jaisor/ProtoPuck32/src/WifiManager.cpp

#if !( defined(ESP32) )
  #error This code is intended to run on ESP32 platform! Please check your Tools->Board setting.
#endif

#include <Arduino.h>
#include <WiFiClient.h>
#include <esp_wifi.h>
#include <ezTime.h>
#include <AsyncElegantOTA.h>
#include <StreamUtils.h>

#include "WifiManager.h"
#include "Configuration.h"

#define MAX_CONNECT_TIMEOUT_MS 15000 // seconds to connect before creating its own AP
#define BOARD_LED_PIN 2

const int RSSI_MAX =-50;// define maximum straighten of signal in dBm
const int RSSI_MIN =-100;// define minimum strength of signal in dBm

WiFiClient espClient;

int dBmtoPercentage(int dBm) {
  int quality;
  if(dBm <= RSSI_MIN) {
  quality = 0;
  } else if(dBm >= RSSI_MAX) {  
  quality = 100;
  } else {
  quality = 2 * (dBm + 100);
  }
  return quality;
}

const unsigned char icon_wifi [] PROGMEM = {
  0x00, 0x00, 0x70, 0x00, 0x7e, 0x00, 0x07, 0x80, 0x01, 0xc0, 0x70, 0xe0, 0x7c, 0x30, 0x0e, 0x38, 
  0x03, 0x18, 0x61, 0x8c, 0x78, 0xcc, 0x1c, 0xc4, 0x0c, 0x66, 0x46, 0x66, 0x66, 0x66, 0x00, 0x00
};

const unsigned char icon_ip [] PROGMEM = {
  0x0, 0xee, 0x49, 0x49, 0x4e, 0x48, 0xe8, 0x0
};

const String htmlTop FL_PROGMEM = "<html>\
  <head>\
  <title>%s</title>\
  <style>\
    body { background-color: #303030; font-family: 'Anaheim',sans-serif; Color: #d8d8d8; }\
  </style>\
  </head>\
  <body>\
  <h1>%s ProtoPuck32</h1>";

const String htmlBottom FL_PROGMEM = "<br><br><hr>\
  <p>Uptime: %02d:%02d:%02d | Device time: %s | Device: %s</p>\
  %s\
  <form method='POST' action='/factory_reset' enctype='application/x-www-form-urlencoded'>\
    <input type='submit' style='font-size: 6pt; color: red; background-color: black;' value='Factory Reset...'>\
  </form>\
  </body>\
</html>";

const String htmlWifiApConnectForm FL_PROGMEM = "<h2>Connect to WiFi Access Point (AP)</h2>\
  <form method='POST' action='/connect' enctype='application/x-www-form-urlencoded'>\
    <label for='ssid'>SSID (AP Name):</label><br>\
    <input type='text' id='ssid' name='ssid'><br><br>\
    <label for='pass'>Password (WPA2):</label><br>\
    <input type='password' id='pass' name='password' minlength='8' autocomplete='off' required><br><br>\
    <input type='submit' value='Connect...'>\
  </form>";

const String htmlDeviceConfigs FL_PROGMEM = "<hr><h2>Configs</h2>\
  <form method='POST' action='/config' enctype='application/x-www-form-urlencoded'>\
    <label for='deviceName'>Device name:</label><br>\
    <input type='text' id='deviceName' name='deviceName' value='%s'><br>\
    <br>\
    <label for='mqttServer'>MQTT Server:</label><br>\
    <input type='text' id='mqttServer' name='mqttServer' value='%s'><br>\
    <label for='mqttPort'>MQTT Port:</label><br>\
    <input type='text' id='mqttPort' name='mqttPort' value='%i'><br>\
    <label for='mqttTopic'>MQTT Topic:</label><br>\
    <input type='text' id='mqttTopic' name='mqttTopic' value='%s'><br>\
    <br>\
    <label for='ntpServer'>NTP Server:</label><br>\
    <input type='text' id='ntpServer' name='ntpServer' value='%s'><br>\
    <label for='gmtOffset_sec'>GMT Offset:</label><br>\
    <input type='text' id='gmtOffset_sec' name='gmtOffset_sec' value='%li'> sec.<br>\
    <label for='daylightOffset_sec'>Daylight Offset:</label><br>\
    <input type='text' id='daylightOffset_sec' name='daylightOffset_sec' value='%i'> sec.<br>\
    <br>\
    <input type='submit' value='Set...'>\
  </form>";

char _deviceId[32];
char *getDeviceId() {
  
  uint32_t chipId = 0;
  for(int i=0; i<17; i=i+8) {
    chipId |= ((ESP.getEfuseMac() >> (40 - i)) & 0xff) << i;
  }

  log_d("Chip ID: '%i'", chipId);

  sprintf_P(_deviceId, "%s_%i", WIFI_FALLBACK_SSID, chipId);

  return _deviceId;
}

CWifiManager::CWifiManager(CDevice * const device)
:apMode(false), rebootNeeded(false), device(device) {  
  pinMode(BOARD_LED_PIN,OUTPUT);
  this->mqtt.setClient(espClient);
  strcpy(SSID, configuration.wifiSsid);
  this->server = new AsyncWebServer(WEB_SERVER_PORT);
  wifiRetries = 0;
  connect();
}

#ifdef OLED
uint16_t CWifiManager::OLED_Status(Adafruit_GFX *oled) {

  wl_status_t s = WiFi.status();
  
  oled->setTextSize(1);
  oled->drawBitmap(0, 0, icon_wifi, 16, 16, 1);

  wifi_mode_t espm;
  esp_wifi_get_mode(&espm);

  if (s == WL_CONNECTED || espm == WIFI_MODE_AP || espm == WIFI_MODE_APSTA) {

  digitalWrite(BOARD_LED_PIN, status == WF_LISTENING ? HIGH : LOW);

  char buf[100];
  int32_t signalPercentage = dBmtoPercentage(WiFi.RSSI());

  if (s == WL_CONNECTED) {
    sprintf(buf, "%s %i%%", WiFi.SSID().c_str(), signalPercentage);
  } else if (espm == WIFI_MODE_AP || espm == WIFI_MODE_APSTA) {
    sprintf(buf, "%s (%i)", softAP_SSID, WiFi.softAPgetStationNum());
  }
  
  oled->setCursor(18,0);
  oled->print(buf);

  oled->drawBitmap(18, 8, icon_ip, 8, 8, 1);
  oled->setCursor(28,8);
  oled->print((s == WL_CONNECTED ? WiFi.localIP() : WiFi.softAPIP()).toString().c_str());

  } else if (status == WF_CONNECTING) {

  unsigned long dt = millis() - tMillis;
  
  oled->setCursor(18,0);
  oled->print(SSID);
  
  oled->drawRect(18, 9, OLED_SCREEN_WIDTH-19, 7, 1);

  uint8_t w = dt * (OLED_SCREEN_WIDTH-21) / MAX_CONNECT_TIMEOUT_MS;
  if (dt >= MAX_CONNECT_TIMEOUT_MS) {
    w = OLED_SCREEN_WIDTH-22;
  }
  oled->fillRect(20, 11, w, 3, 1);

  digitalWrite(BOARD_LED_PIN, dt % 100 ? LOW : HIGH);
  }  else {
  digitalWrite(BOARD_LED_PIN, LOW);
  }
  
  //

  return 100;
}
#endif

void CWifiManager::connect() {

  status = WF_CONNECTING;
  strcpy(softAP_SSID, "");
  tMillis = millis();

  if (strlen(SSID)) {

    // Join AP from Config
    log_d("Connecting to WiFi: '%s'", SSID);
    WiFi.begin(SSID, configuration.wifiPassword);
    apMode = false;
    wifiRetries = 0;
  
  } else {

    strcpy(softAP_SSID, getDeviceId());
    log_i("Creating WiFi: '%s' / '%s'", softAP_SSID, WIFI_FALLBACK_PASS);
    
    if (WiFi.softAP(softAP_SSID, WIFI_FALLBACK_PASS)) {
      wifiRetries = 0;
      apMode = true;
      log_i("Wifi AP '%s' created, listening on '%s'", softAP_SSID, WiFi.softAPIP().toString().c_str());
    } else {
      log_e("Wifi AP faliled");
    };
    
    WiFi.softAP(softAP_SSID, WIFI_FALLBACK_PASS);
  }
  
}

void CWifiManager::listen() {

  status = WF_LISTENING;

  // Web
  server->on("/", std::bind(&CWifiManager::handleRoot, this, std::placeholders::_1));
  server->on("/connect", HTTP_POST, std::bind(&CWifiManager::handleConnect, this, std::placeholders::_1));
  server->on("/config", HTTP_POST, std::bind(&CWifiManager::handleConfig, this, std::placeholders::_1));
  server->on("/factory_reset", HTTP_POST, std::bind(&CWifiManager::handleFactoryReset, this, std::placeholders::_1));
  server->begin();
  Log.infoln("Web server listening on %s port %i", WiFi.localIP().toString().c_str(), WEB_SERVER_PORT);

  sensorJson["ip"] = WiFi.localIP();
  
  // NTP
  log_i("Configuring time from %s at %i (%i)", configuration.ntpServer, configuration.gmtOffset_sec, configuration.daylightOffset_sec);

  // OTA
  AsyncElegantOTA.begin(server);

  // MQTT
  mqtt.setServer(configuration.mqttServer, configuration.mqttPort);
  
  using std::placeholders::_1;
  using std::placeholders::_2;
  using std::placeholders::_3;
  mqtt.setCallback(std::bind( &CWifiManager::mqttCallback, this, _1,_2,_3));

  if (!mqtt.connected()) {
    log_d("Attempting MQTT connection to '%s:%i' ...", configuration.mqttServer, configuration.mqttPort);
    if (mqtt.connect("arduinoClient")) {
      log_i("MQTT connected");
      postSensorUpdate();
      // ... and resubscribe
      //client.subscribe("inTopic");
    } else {
      log_d("MQTT connect failed, rc=%i", mqtt.state());
    }
  }

  configTime(configuration.gmtOffset_sec, configuration.daylightOffset_sec, configuration.ntpServer);
  struct tm timeinfo;
  //time()
  if(getLocalTime(&timeinfo)){
    log_i("The time is %i:%i", timeinfo.tm_hour,timeinfo.tm_min);
    CONFIG_updateLedBrightnessTime();
  }
  
}

void CWifiManager::loop() {

  if (rebootNeeded && millis() - tMillis > 200) {
  log_i("Rebooting...");
#ifdef ESP32
  ESP.restart();
#elif ESP8266
  ESP.reset();
#endif
  return;
  }

  if (WiFi.status() == WL_CONNECTED || apMode ) {
  // WiFi is connected

  if (status != WF_LISTENING) {  
    // Start listening for requests
    listen();
  }

  // Send sensor updates periodically
  if (millis() - tMillis > 60000) {
    tMillis = millis();
    postSensorUpdate();
  }

  } else {
  // WiFi is down

  switch (status) {
    case WF_LISTENING: {
      log_i("Disconnecting %i", status);
      server->end();
      tMillis = millis();
      status = WF_CONNECTING;
      connect();
    } break;
    case WF_CONNECTING: {
      if (millis() - tMillis > MAX_CONNECT_TIMEOUT_MS) {
        tMillis = millis();
        if (wifiRetries++ > 3) {
          log_w("Connecting failed (wifi status %i) after %l ms, create an AP instead", (millis() - tMillis), WiFi.status());
          strcpy(SSID, "");
        }
        connect();
      }
    } break;

  }

  }
  
}

void CWifiManager::handleRoot(AsyncWebServerRequest *request) {

  log_i("handleRoot");
  
  int sec = millis() / 1000;
  int min = sec / 60;
  int hr = min / 60;

  AsyncResponseStream *response = request->beginResponseStream("text/html");
  response->printf(htmlTop.c_str(), configuration.name, configuration.name);

  if (apMode) {
  response->printf(htmlWifiApConnectForm.c_str());
  } else {
  response->printf("<p>Connected to '%s'</p>", SSID);
  }
  
  String modeOptions = "";
  
  response->printf(htmlDeviceConfigs.c_str(), configuration.name, configuration.mqttServer, 
  configuration.mqttPort, configuration.mqttTopic, configuration.ntpServer, configuration.gmtOffset_sec, configuration.daylightOffset_sec);

  char dTime[100] = "";
  struct tm timeinfo;
  if(getLocalTime(&timeinfo)) {
    strftime(dTime, 100, "%F %T %z", &timeinfo);
  }

  response->printf(htmlBottom.c_str(), hr, min % 60, sec % 60, dTime, String(DEVICE_NAME), getTempSensorResponse().c_str());
  request->send(response);
}

void CWifiManager::handleConnect(AsyncWebServerRequest *request) {

  log_i("handleConnect");

  String ssid = request->arg("ssid");
  String password = request->arg("password");
  
  int sec = millis() / 1000;
  int min = sec / 60;
  int hr = min / 60;

  char dTime[100] = "";
  struct tm timeinfo;
  if(getLocalTime(&timeinfo)) {
    strftime(dTime, 100, "%F %T %z", &timeinfo);
  }

  AsyncResponseStream *response = request->beginResponseStream("text/html");
  response->printf(htmlTop.c_str(), configuration.name, configuration.name);
  response->printf("<p>Connecting to '%s' ... see you on the other side!</p>", ssid.c_str());
  response->printf(htmlBottom.c_str(), hr, min % 60, sec % 60, dTime, String(DEVICE_NAME), getTempSensorResponse().c_str());
  request->send(response);

  ssid.toCharArray(configuration.wifiSsid, sizeof(configuration.wifiSsid));
  password.toCharArray(configuration.wifiPassword, sizeof(configuration.wifiPassword));

  log_i("Saved config SSID: '%s'", configuration.wifiSsid);

  EEPROM_saveConfig();

  strcpy(SSID, configuration.wifiSsid);
  connect();
}

void CWifiManager::handleConfig(AsyncWebServerRequest *request) {

  log_i("handleConfig");

  String deviceName = request->arg("deviceName");
  deviceName.toCharArray(configuration.name, sizeof(configuration.name));
  log_i("Device req name: %s", deviceName);
  log_i("Device size %i name: %s", sizeof(configuration.name), configuration.name);

  String mqttServer = request->arg("mqttServer");
  mqttServer.toCharArray(configuration.mqttServer, sizeof(configuration.mqttServer));
  log_i("MQTT Server: %s", mqttServer);

  uint16_t mqttPort = atoi(request->arg("mqttPort").c_str());
  configuration.mqttPort = mqttPort;
  log_i("MQTT Port: %i", mqttPort);

  String mqttTopic = request->arg("mqttTopic");
  mqttTopic.toCharArray(configuration.mqttTopic, sizeof(configuration.mqttTopic));
  log_i("MQTT Topic: %s", mqttTopic);

  String ntpServer = request->arg("ntpServer");
  ntpServer.toCharArray(configuration.ntpServer, sizeof(configuration.ntpServer));
  log_i("ntpServer: %s", ntpServer);

  long gmtOffset_sec = atol(request->arg("gmtOffset_sec").c_str());
  configuration.gmtOffset_sec = gmtOffset_sec;
  log_i("gmtOffset_sec: %l", gmtOffset_sec);

  int daylightOffset_sec = atoi(request->arg("daylightOffset_sec").c_str());
  configuration.daylightOffset_sec = daylightOffset_sec;
  log_i("daylightOffset_sec: %i", daylightOffset_sec);

  configTime(configuration.gmtOffset_sec, configuration.daylightOffset_sec, configuration.ntpServer);
  struct tm timeinfo;
  if(getLocalTime(&timeinfo)){
    log_i("The time is %i:%i", timeinfo.tm_hour,timeinfo.tm_min);
    CONFIG_updateLedBrightnessTime();
  }

  EEPROM_saveConfig();

  // TODO check if MQTT reconnect is needed
  if (strlen(configuration.mqttServer) && strlen(configuration.mqttTopic)) {
    rebootNeeded = true;
  }

  request->redirect("/");
}

String CWifiManager::getTempSensorResponse() {
#ifdef TEMP_SENSOR
  float temp = device->temperature();
  bool tempInC = false;
  return String("<div>\
  Temperature: " + String(tempInC ? temp : (temp*1.8)+32, 1) + (tempInC ? "C" : "F") +"<br/>\
  Hunidity: " + String(device->humidity(), 1) + "% <br/>\
  </div>");
#else
  return "";
#endif
}

void CWifiManager::postSensorUpdate() {
  if (!mqtt.connected()) {
    if (mqtt.state() < MQTT_CONNECTED 
      && strlen(configuration.mqttServer) && strlen(configuration.mqttTopic)) { // Reconnectable
      log_d("Attempting to reconnect from MQTT state %i at '%s:%i' ...", mqtt.state(), configuration.mqttServer, configuration.mqttPort);
      if (mqtt.connect("arduinoClient")) {
        log_i("MQTT reconnected");
      } else {
        log_w("MQTT reconnect failed, rc=%i", mqtt.state());
      }
    }
    if (!mqtt.connected()) {
      log_d("MQTT not connected %i", mqtt.state());
      return;
    }
  }

  if (!strlen(configuration.mqttTopic)) {
    log_w("Blank MQTT topic");
    return;
  }

  char topic[255];
  bool current;
  float v; int iv;

  bool pJson = configuration.mqttDataType == MQTT_DATA_JSON || configuration.mqttDataType == MQTT_DATA_BOTH;
  bool pScalar = configuration.mqttDataType == MQTT_DATA_SCALAR || configuration.mqttDataType == MQTT_DATA_BOTH;

#ifdef TEMP_SENSOR
  float vt = device->temperature();
  float vh = device->humidity();

  if (configuration.tempUnit == TEMP_UNIT_FAHRENHEIT) {
    vt = vt * 1.8 + 32;
  }

  if (pScalar) {
    sprintf_P(topic, "%s/temperature", configuration.mqttTopic);
    mqtt.publish(topic,String(v, 2).c_str());
    log_d("Sent '%F%s' temp to MQTT topic '%s'", vt, configuration.tempUnit == TEMP_UNIT_FAHRENHEIT ? "F" : "C", topic);
  
    sprintf_P(topic, "%s/humidity", configuration.mqttTopic);
    mqtt.publish(topic,String(v, 2).c_str());
    log_d("Sent '%F%%' humidity to MQTT topic '%s'", vh, topic);
  }

  if (pJson) {
    char tunit[32];
    snprintf(tunit, 32, (configuration.tempUnit == TEMP_UNIT_CELSIUS ? "Celsius" : (configuration.tempUnit == TEMP_UNIT_FAHRENHEIT ? "Fahrenheit" : "" )));

    sensorJson["temperature"] = vt;
    sensorJson["temperature_unit"] = tunit;
    sensorJson["humidity"] = vh;
    sensorJson["humidit_unit"] = "percent";
    sensorJson["ledBrightness"] = configuration.ledBrightness;
    
  }
#endif

#ifdef BATTERY_SENSOR
  if (configuration.battVoltsDivider > 0) {
  v = (float)(batteryVoltage + sensorProvider->getBatteryVoltage(NULL)) / 2.0;
  if (pScalar) {
    sprintf_P(topic, "%s/battery", configuration.mqttTopic);
    mqtt.publish(topic,String(v, 2).c_str());
    Log.noticeln("Sent '%Fv' battery voltage to MQTT topic '%s'", v, topic);
  }
  if (pJson) {
    sensorJson["battery_v"] = v;
  }

  iv = analogRead(BATTERY_SENSOR_ADC_PIN);
  if (pScalar) {
    sprintf_P(topic, "%s/adc_raw", configuration.mqttTopic);
    mqtt.publish(topic,String(iv).c_str());
    Log.noticeln("Sent '%i' raw ADC value to MQTT topic '%s'", iv, topic);
  }
  if (pJson) {
    sensorJson["adc_raw"] = iv;
  }
  }
#endif

  if (WiFi.getMode() != WIFI_AP) {
    iv = dBmtoPercentage(WiFi.RSSI());
    if (pScalar) {
      sprintf_P(topic, "%s/wifi_percent", configuration.mqttTopic);
      mqtt.publish(topic,String(iv).c_str());
      Log.noticeln("Sent '%i%' WiFI signal to MQTT topic '%s'", iv, topic);
    }
    if (pJson) {
      sensorJson["wifi_percent"] = iv;
      sensorJson["wifi_rssi"] = WiFi.RSSI();
    }
  }

  time_t now; 
  time(&now);
  
  if (pScalar) {
    sprintf_P(topic, "%s/timestamp", configuration.mqttTopic);
    mqtt.publish(topic,String(now).c_str());
    Log.noticeln("Sent '%u' timestamp to MQTT topic '%s'", (unsigned long)now, topic);
  }
  
  if (pJson) {
    // Convert to ISO8601 for JSON
    char buf[sizeof "2011-10-08T07:07:09Z"];
    strftime(buf, sizeof buf, "%FT%TZ", gmtime(&now));
    sensorJson["timestamp_iso8601"] = String(buf);

    // sensor Json
    sprintf_P(topic, "%s/json", configuration.mqttTopic);
    mqtt.beginPublish(topic, measureJson(sensorJson), false);
    BufferingPrint bufferedClient(mqtt, 32);
    serializeJson(sensorJson, bufferedClient);
    bufferedClient.flush();
    mqtt.endPublish();

    String jsonStr;
    serializeJson(sensorJson, jsonStr);
    Log.noticeln("Sent '%s' json to MQTT topic '%s'", jsonStr.c_str(), topic);
  }
}

#ifdef LED_EXTERNAL_MATRIX
/*
  Post body should contain comma delimited items in a list like this: X Y RRGGBB,X Y RRGGBB
  Each item is a space delimited X,Y coordinates of the LED pixel in the matrix and the expected color in Hex
  Ex: 0 0 ffbbdd,1 0 c91232
*/
void CWifiManager::handleLEDMatrix() {
  /*
  digitalWrite(BOARD_LED_PIN, LOW);

  //matrix_pixel_t pixels[LED_EXTERNAL_MATRIX_WIDTH * LED_EXTERNAL_MATRIX_HEIGHT];

  String postBody = server->arg("plain");
  log_d("LED Matrinx: %s", postBody.c_str());

  //ioTManager->setLeds(pixels);

/*
  const char pixelDelimiter[1] = ",";
  const char *raw = postBody.c_str();
  char *pixelToken = strtok(raw, pixelDelimiter);

  while( pixelToken != NULL ) {
  log_d("P: '%s'", pixelToken);
  pixelToken = strtok(NULL, pixelDelimiter);
  }
*/
  
  //postBody.indexOf()
  
/*
  
  server->send(200, "text/html", "OK");
  digitalWrite(BOARD_LED_PIN, HIGH);
  */
}
#endif

void CWifiManager::handleFactoryReset(AsyncWebServerRequest *request) {
  Log.infoln("handleFactoryReset");
  
  AsyncResponseStream *response = request->beginResponseStream("text/html");
  response->setCode(200);
  response->printf("OK");

  EEPROM_wipe();
  rebootNeeded = true;
  
  request->send(response);
}

void CWifiManager::mqttCallback(char *topic, uint8_t *payload, unsigned int length) {

  if (length == 0) {
    return;
  }

  Log.noticeln("Received %u bytes message on MQTT topic '%s'", length, topic);
  if (!strcmp(topic, mqttSubcribeTopicConfig)) {
    deserializeJson(configJson, (const byte*)payload, length);

    String jsonStr;
    serializeJson(configJson, jsonStr);
    Log.noticeln("Received configuration over MQTT with json: '%s'", jsonStr.c_str());

    if (configJson.containsKey("ledBrightness")) {
      configuration.ledBrightness = configJson["ledBrightness"].as<float>();
    }

    if (configJson.containsKey("name")) {
      strncpy(configuration.name, configJson["name"], 128);
    }

    if (configJson.containsKey("mqttTopic")) {
      strncpy(configuration.mqttTopic, configJson["mqttTopic"], 64);
    }

    // Delete the config message in case it was retained
    mqtt.publish(mqttSubcribeTopicConfig, NULL, 0, true);
    Log.noticeln("Deleted config message");

    EEPROM_saveConfig();
    postSensorUpdate();
  }
  
}
