jaisor/ProtoPuck32/include/InternalLEDManager.h

#ifndef _INTERNAL_LED_MANAGER_H
#define _INTERNAL_LED_MANAGER_H

#include <vector>
#include "LEDManager.h"

class CInternalLEDManager: public CLEDManager {

private:
    uint8_t startIndex = 0;
    unsigned long tMillis, tMillsChangePalette;

    std::vector<CRGBPalette16> palettes;
    uint8_t currentPaletteIndex;
    uint8_t changePalette;

public:
	CInternalLEDManager(uint16_t size, float brightness);

#ifdef OLED
    virtual uint16_t OLED_Status(Adafruit_GFX *oled);
#endif
#ifdef LED
    virtual uint16_t LED_Status(CRGB *leds);
#endif
#ifdef KEYPAD
    virtual void keyEvent(key_status_t key);
#endif

    virtual void loop();
};

#endif
