jaisor/ProtoPuck32/include/LEDManager.h

#ifndef _LED_MANAGER_H
#define _LED_MANAGER_H

#include "BaseManager.h"
#ifdef LED
    #include <FastLED.h>
#endif

class CLEDManager: public CBaseManager {

protected:
    const uint16_t size;
    float_t brightness;
    float_t brightnessChange;

public:
	CLEDManager(const uint16_t size, float brightness);

#ifdef LED
    virtual uint16_t LED_Status(CRGB *leds) { return 0; };
#endif

    virtual void loop() {};
};

#endif
