jaisor/ProtoPuck32/src/MatrixLEDManager.cpp

#include <Arduino.h>
#include "MatrixLEDManager.h"
#include "matrix/MatrixModeRGBDemo.h"
#include "matrix/MatrixModeMovingSquare.h"
#include "matrix/MatrixModePicture.h"
#include "matrix/MatrixModeGameOfLife.h"
#include "matrix/MatrixModePixel.h"
#include "matrix/MatrixModeFallingStars.h"
#include "matrix/MatrixModeClock.h"
#include "matrix/MatrixModeFireworks.h"
#include "matrix/MatrixModeSoundLevel.h"

#include "matrix/bitmaps.h"

#ifdef LED_EXTERNAL_MATRIX

CMatrixLEDManager::CMatrixLEDManager(CRGB *leds, const uint8_t width, const uint8_t height, float brightness)
: CLEDManager(width * height, brightness), width(width), height(height) {

    this->leds = leds;

    tMillis = tMillsChangeMode = millis();

#ifdef MIC_I2S
    modes.push_back(new CMatrixModeSoundLevel(width, height));
#endif
    modes.push_back(new CMatrixModeClock(width, height));
    //modes.push_back(new CMatrixModeFireworks(width, height));
    modes.push_back(new CMatrixModeFallingStars(width, height));
    modes.push_back(new CMatrixModePixel(width, height));
    modes.push_back(new CMatrixModeGameOfLife(width, height));
    modes.push_back(new CMatrixModePicture(width, height, BITMAP_BDAY, BITMAPS_BDAY));
    modes.push_back(new CMatrixModeRGBDemo(width, height));
    modes.push_back(new CMatrixModeMovingSquare(width, height));
    modes.push_back(new CMatrixModePicture(width, height, BITMAP_MINECRAFT, BITMAPS_MINECRAFT));
    

    currentModeIndex = 0;
}

void CMatrixLEDManager::loop() {
    if (changeMode && millis() - tMillsChangeMode > 1000) {
        tMillsChangeMode = millis();
        currentModeIndex += changeMode;
        if (currentModeIndex < 0 ) {
            currentModeIndex = modes.size()-1;
        }
        if (currentModeIndex >= modes.size()) {
            currentModeIndex = 0;
        }
        log_d("Change mode %i changed index to %i", changeMode, currentModeIndex);
    }
    changeMode = 0;

    modes[currentModeIndex]->draw(leds);
}

#ifdef KEYPAD
void CMatrixLEDManager::keyEvent(key_status_t key) {
    switch (key) {
        case KEY_LEFT: changeMode = 1; break;
        case KEY_RIGHT: changeMode = -1; break;
        default: changeMode = 0;
    }

    modes[currentModeIndex]->keyEvent(key);
}
#endif

#ifdef OLED
uint16_t CMatrixLEDManager::OLED_Status(Adafruit_GFX *oled) {
    /*
    oled->setTextSize(1);
    oled->setCursor(00, 16);
    char buf[50];
    sprintf(buf, "%0.2f:%0.2f", xf, yf);
    oled->print(buf);
    */
    return 0;
}
#endif

#endif
